MidwestMotorBoy/Battery-Bank/BatteryBank.kicad_sch

## KiCad design BatteryBank.kicad_sch (2026-10-09, an earlier design)

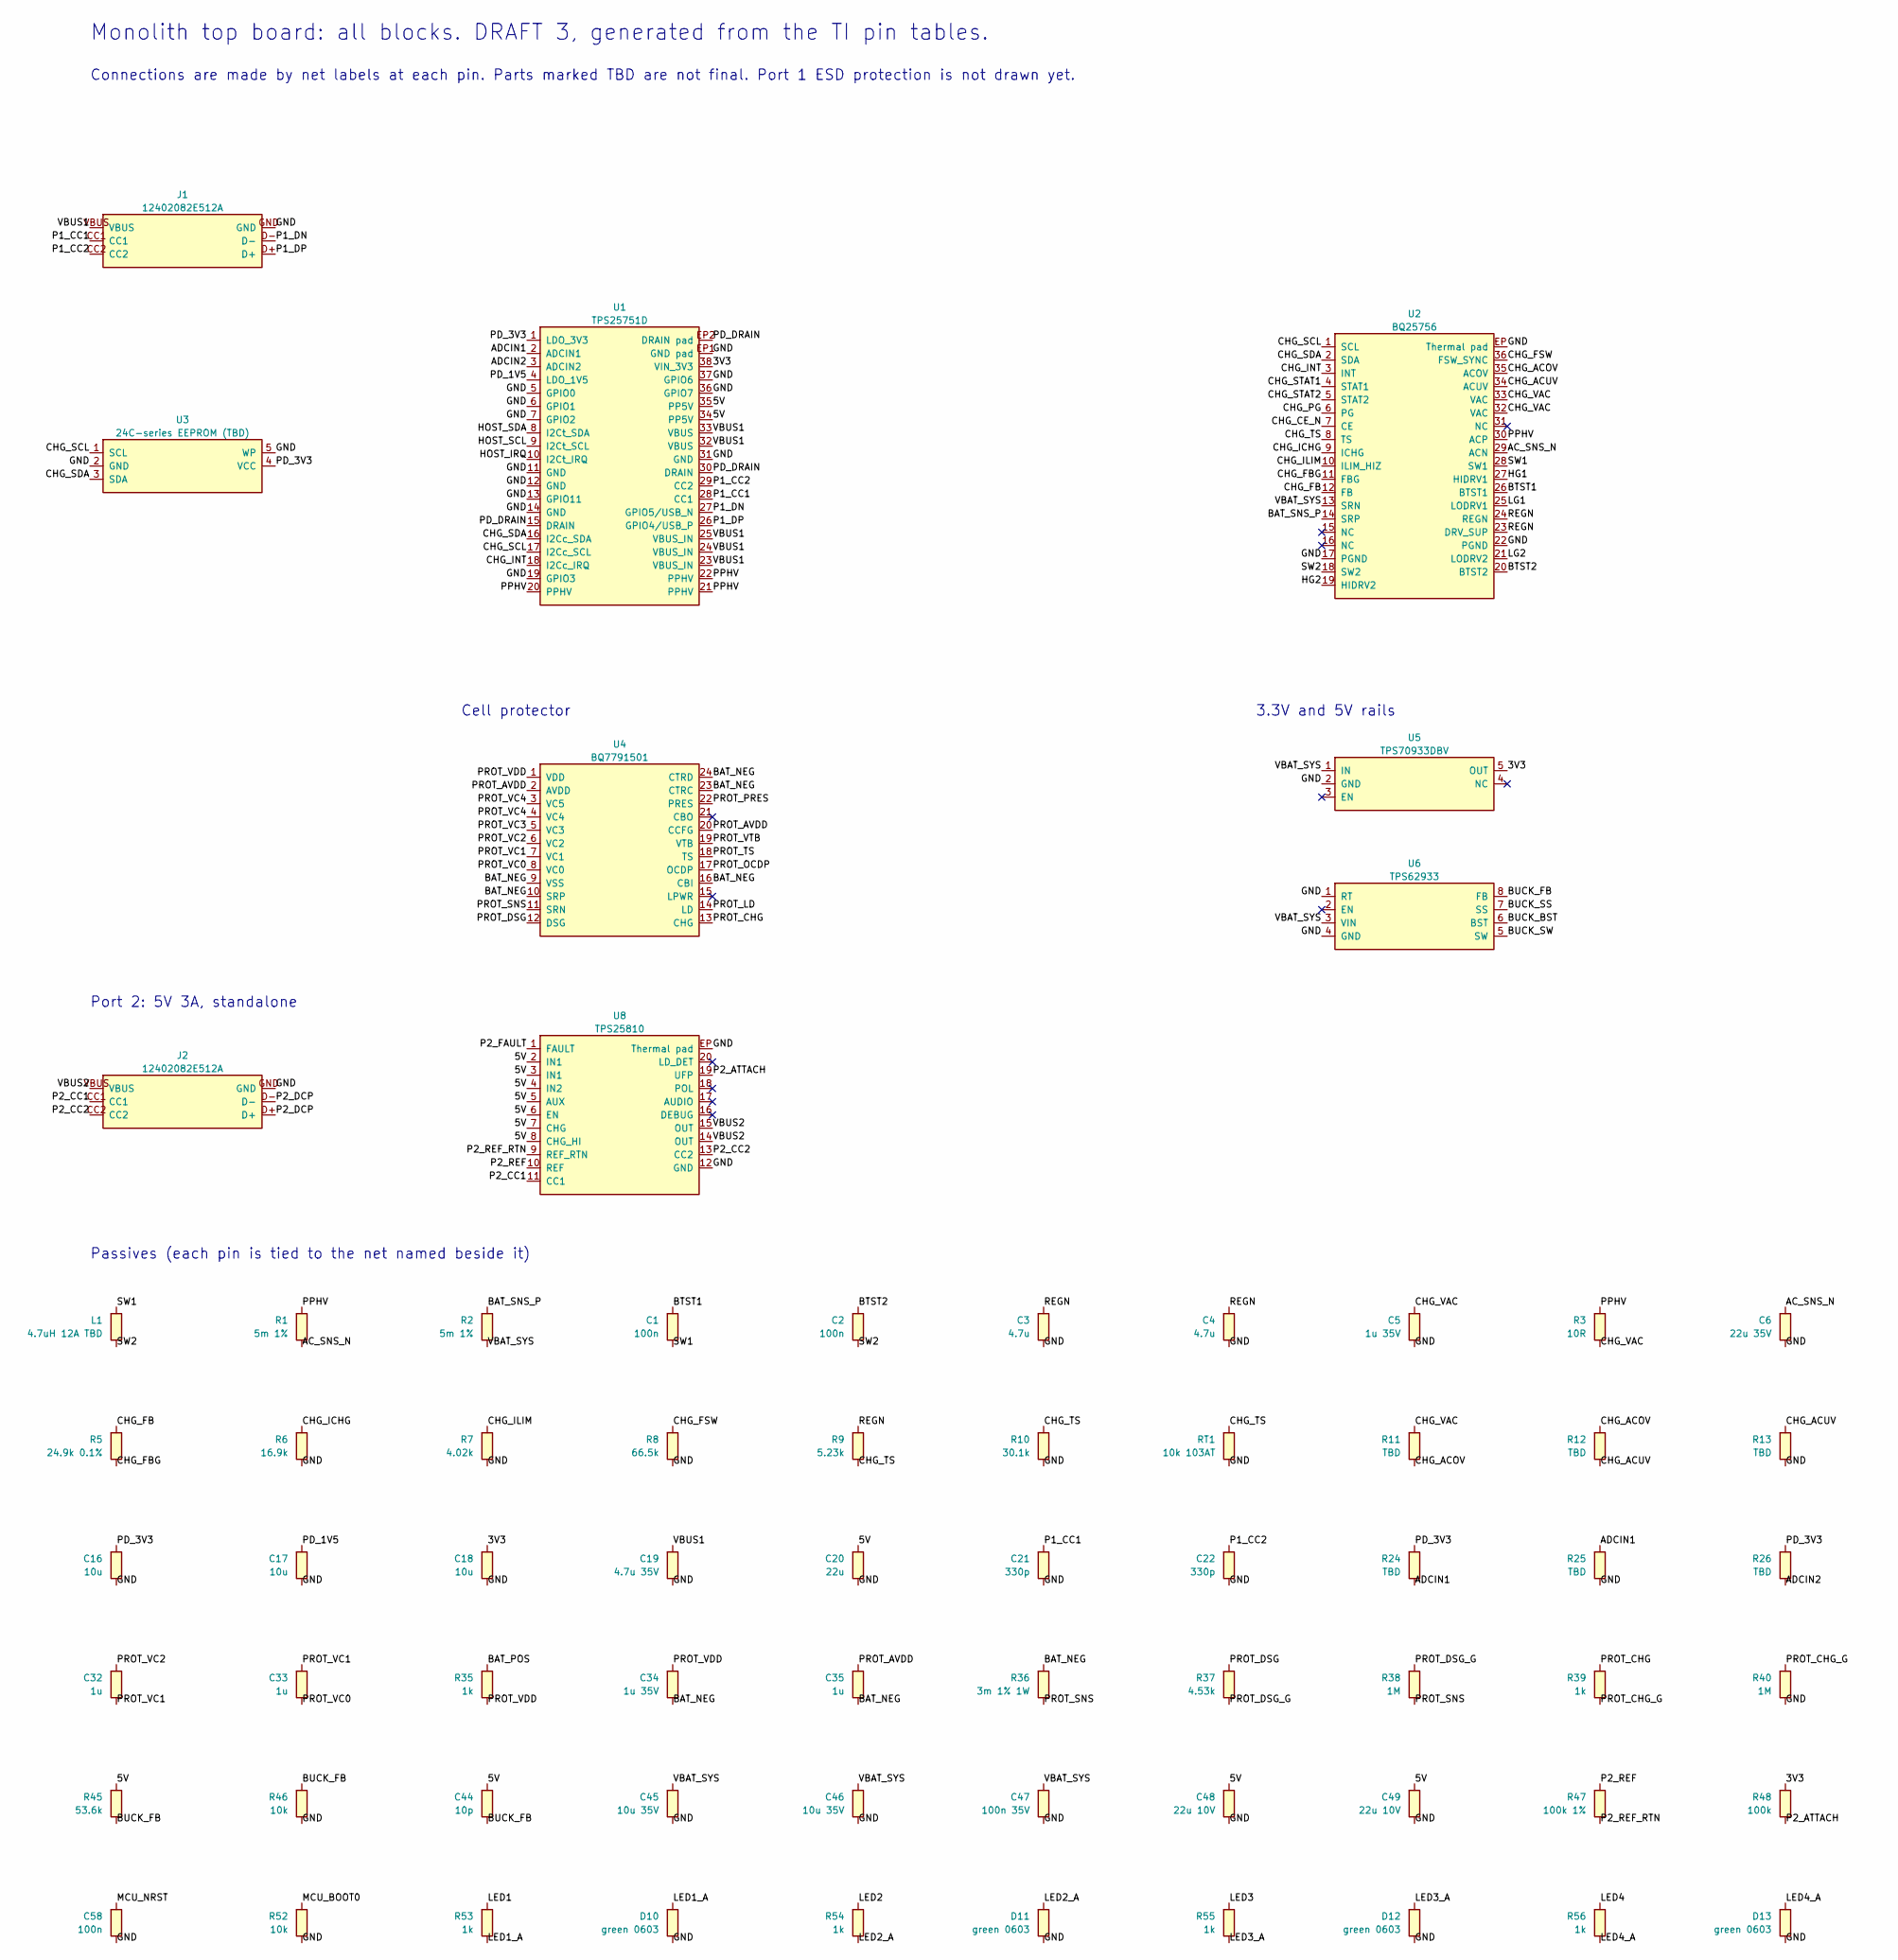
[picture p9: schematic BatteryBank.kicad_sch, part in row 1, column 1]

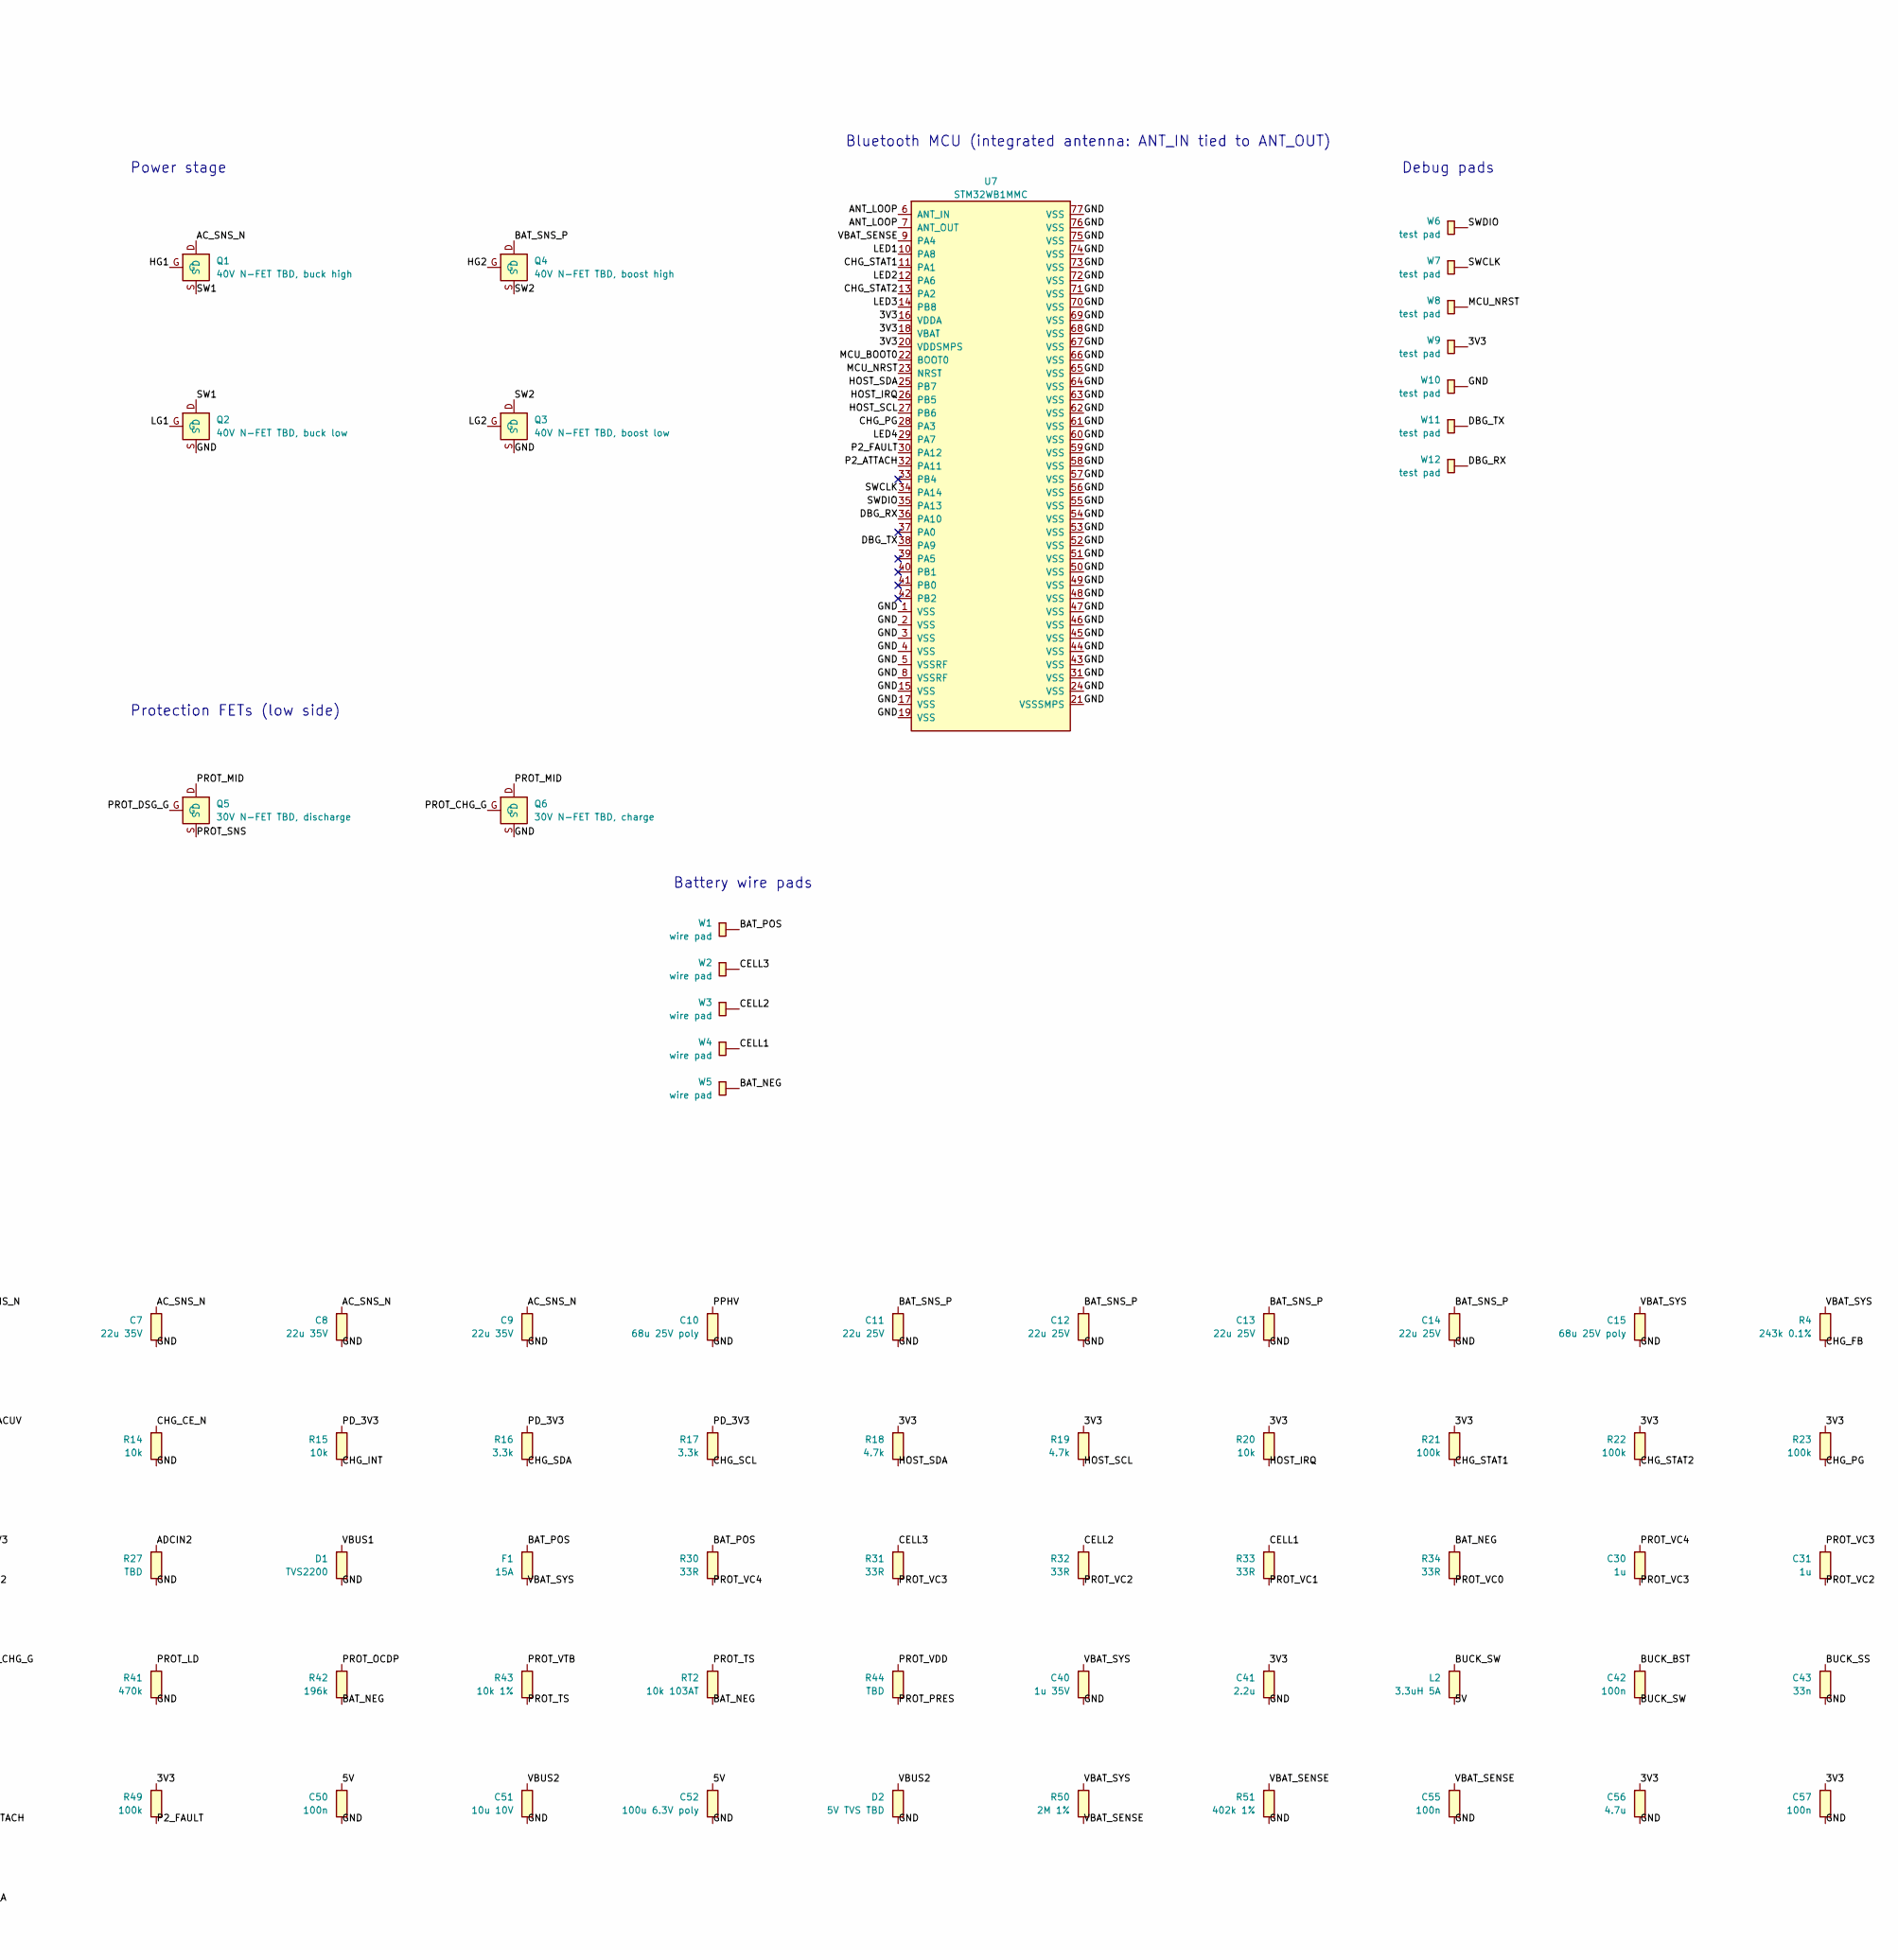
[picture p10: schematic BatteryBank.kicad_sch, part in row 1, column 2]

Parts:
C1, C2, C42, C50, C55, C57, C58: 100n
C3, C4, C56: 4.7u
C5, C34, C40: 1u 35V
C6, C7, C8, C9: 22u 35V
C10, C15: 68u 25V poly
C11, C12, C13, C14: 22u 25V
C16, C17, C18: 10u
C19: 4.7u 35V
C20: 22u
C21, C22: 330p
C30, C31, C32, C33, C35: 1u
C41: 2.2u
C43: 33n
C44: 10p
C45, C46: 10u 35V
C47: 100n 35V
C48, C49: 22u 10V
C51: 10u 10V
C52: 100u 6.3V poly
D1: TVS2200
D2: 5V TVS TBD
D10, D11, D12, D13: green 0603
F1: 15A
J1, J2: 12402082E512A
L1: 4.7uH 12A TBD
L2: 3.3uH 5A
Q1: 40V N-FET TBD, buck high
Q2: 40V N-FET TBD, buck low
Q3: 40V N-FET TBD, boost low
Q4: 40V N-FET TBD, boost high
Q5: 30V N-FET TBD, discharge
Q6: 30V N-FET TBD, charge
R1, R2: 5m 1%
R3: 10R
R4: 243k 0.1%
R5: 24.9k 0.1%
R6: 16.9k
R7: 4.02k
R8: 66.5k
R9: 5.23k
R10: 30.1k
R11, R12, R13, R24, R25, R26, R27, R44: TBD
R14, R15, R20, R46, R52: 10k
R16, R17: 3.3k
R18, R19: 4.7k
R21, R22, R23, R48, R49: 100k
R30, R31, R32, R33, R34: 33R
R35, R39, R53, R54, R55, R56: 1k
R36: 3m 1% 1W
R37: 4.53k
R38, R40: 1M
R41: 470k
R42: 196k
R43: 10k 1%
R45: 53.6k
R47: 100k 1%
R50: 2M 1%
R51: 402k 1%
RT1, RT2: 10k 103AT
U1: TPS25751D
U2: BQ25756
U3: 24C-series EEPROM (TBD)
U4: BQ7791501
U5: TPS70933DBV
U6: TPS62933
U7: STM32WB1MMC
U8: TPS25810
W1, W2, W3, W4, W5: wire pad
W6, W7, W8, W9, W10, W11, W12: test pad

Connections:
3V3: C18.1, C41.1, C56.1, C57.1, R18.1, R19.1, R20.1, R21.1, R22.1, R23.1, R48.1, R49.1, U1.38 (VIN_3V3), U5.5 (OUT), U7.16 (VDDA), U7.18 (VBAT), U7.20 (VDDSMPS), W9.1
5V: C20.1, C44.1, C48.1, C49.1, C50.1, C52.1, L2.2, R45.1, U1.34 (PP5V), U1.35 (PP5V), U8.2 (IN1), U8.3 (IN1), U8.4 (IN2), U8.5 (AUX), U8.6 (EN), U8.7 (CHG), U8.8 (CHG_HI)
AC_SNS_N: C6.1, C7.1, C8.1, C9.1, Q1.D, R1.2, U2.29 (ACN)
ADCIN1: R24.2, R25.1, U1.2 (ADCIN1)
ADCIN2: R26.2, R27.1, U1.3 (ADCIN2)
ANT_LOOP: U7.6 (ANT_IN), U7.7 (ANT_OUT)
BAT_NEG: C34.2, C35.2, R34.1, R36.1, R42.2, RT2.2, U4.9 (VSS), U4.10 (SRP), U4.16 (CBI), U4.23 (CTRC), U4.24 (CTRD), W5.1
BAT_POS: F1.1, R30.1, R35.1, W1.1
BAT_SNS_P: C11.1, C12.1, C13.1, C14.1, Q4.D, R2.1, U2.14 (SRP)
BTST1: C1.1, U2.26 (BTST1)
BTST2: C2.1, U2.20 (BTST2)
BUCK_BST: C42.1, U6.6 (BST)
BUCK_FB: C44.2, R45.2, R46.1, U6.8 (FB)
BUCK_SS: C43.1, U6.7 (SS)
BUCK_SW: C42.2, L2.1, U6.5 (SW)
CELL1: R33.1, W4.1
CELL2: R32.1, W3.1
CELL3: R31.1, W2.1
CHG_ACOV: R11.2, R12.1, U2.35 (ACOV)
CHG_ACUV: R12.2, R13.1, U2.34 (ACUV)
CHG_CE_N: R14.1, U2.7 (CE)
CHG_FB: R4.2, R5.1, U2.12 (FB)
CHG_FBG: R5.2, U2.11 (FBG)
CHG_FSW: R8.1, U2.36 (FSW_SYNC)
CHG_ICHG: R6.1, U2.9 (ICHG)
CHG_ILIM: R7.1, U2.10 (ILIM_HIZ)
CHG_INT: R15.2, U1.18 (I2Cc_IRQ), U2.3 (INT)
CHG_PG: R23.2, U2.6 (PG), U7.28 (PA3)
CHG_SCL: R17.2, U1.17 (I2Cc_SCL), U2.1 (SCL), U3.1 (SCL)
CHG_SDA: R16.2, U1.16 (I2Cc_SDA), U2.2 (SDA), U3.3 (SDA)
CHG_STAT1: R21.2, U2.4 (STAT1), U7.11 (PA1)
CHG_STAT2: R22.2, U2.5 (STAT2), U7.13 (PA2)
CHG_TS: R9.2, R10.1, RT1.1, U2.8 (TS)
CHG_VAC: C5.1, R3.2, R11.1, U2.32 (VAC), U2.33 (VAC)
DBG_RX: U7.36 (PA10), W12.1
DBG_TX: U7.38 (PA9), W11.1
GND: C3.2, C4.2, C5.2, C6.2, C7.2, C8.2, C9.2, C10.2, C11.2, C12.2, C13.2, C14.2, C15.2, C16.2, C17.2, C18.2, C19.2, C20.2, C21.2, C22.2, C40.2, C41.2, C43.2, C45.2, C46.2, C47.2, C48.2, C49.2, C50.2, C51.2, C52.2, C55.2, C56.2, C57.2, C58.2, D1.2, D2.2, D10.2, D11.2, D12.2, D13.2, J1.GND, J2.GND, Q2.S, Q3.S, Q6.S, R6.2, R7.2, R8.2, R10.2, R13.2, R14.2, R25.2, R27.2, R40.2, R41.2, R46.2, R51.2, R52.2, RT1.2, U1.5 (GPIO0), U1.6 (GPIO1), U1.7 (GPIO2), U1.11 (GND), U1.12 (GND), U1.13 (GPIO11), U1.14 (GND), U1.19 (GPIO3), U1.31 (GND), U1.36 (GPIO7), U1.37 (GPIO6), U1.EP1 (GND pad), U2.17 (PGND), U2.22 (PGND), U2.EP (Thermal pad), U3.2 (GND), U3.5 (WP), U5.2 (GND), U6.1 (RT), U6.4 (GND), U7.1 (VSS), U7.2 (VSS), U7.3 (VSS), U7.4 (VSS), U7.5 (VSSRF), U7.8 (VSSRF), U7.15 (VSS), U7.17 (VSS), U7.19 (VSS), U7.21 (VSSSMPS), U7.24 (VSS), U7.31 (VSS), U7.43 (VSS), U7.44 (VSS), U7.45 (VSS), U7.46 (VSS), U7.47 (VSS), U7.48 (VSS), U7.49 (VSS), U7.50 (VSS), U7.51 (VSS), U7.52 (VSS), U7.53 (VSS), U7.54 (VSS), U7.55 (VSS), U7.56 (VSS), U7.57 (VSS), U7.58 (VSS), U7.59 (VSS), U7.60 (VSS), U7.61 (VSS), U7.62 (VSS), U7.63 (VSS), U7.64 (VSS), U7.65 (VSS), U7.66 (VSS), U7.67 (VSS), U7.68 (VSS), U7.69 (VSS), U7.70 (VSS), U7.71 (VSS), U7.72 (VSS), U7.73 (VSS), U7.74 (VSS), U7.75 (VSS), U7.76 (VSS), U7.77 (VSS), U8.12 (GND), U8.EP (Thermal pad), W10.1
HG1: Q1.G, U2.27 (HIDRV1)
HG2: Q4.G, U2.19 (HIDRV2)
HOST_IRQ: R20.2, U1.10 (I2Ct_IRQ), U7.26 (PB5)
HOST_SCL: R19.2, U1.9 (I2Ct_SCL), U7.27 (PB6)
HOST_SDA: R18.2, U1.8 (I2Ct_SDA), U7.25 (PB7)
LED1: R53.1, U7.10 (PA8)
LED1_A: D10.1, R53.2
LED2: R54.1, U7.12 (PA6)
LED2_A: D11.1, R54.2
LED3: R55.1, U7.14 (PB8)
LED3_A: D12.1, R55.2
LED4: R56.1, U7.29 (PA7)
LED4_A: D13.1, R56.2
LG1: Q2.G, U2.25 (LODRV1)
LG2: Q3.G, U2.21 (LODRV2)
MCU_BOOT0: R52.1, U7.22 (BOOT0)
MCU_NRST: C58.1, U7.23 (NRST), W8.1
P1_CC1: C21.1, J1.CC1, U1.28 (CC1)
P1_CC2: C22.1, J1.CC2, U1.29 (CC2)
P1_DN: J1.D-, U1.27 (GPIO5/USB_N)
P1_DP: J1.D+, U1.26 (GPIO4/USB_P)
P2_ATTACH: R48.2, U7.32 (PA11), U8.19 (UFP)
P2_CC1: J2.CC1, U8.11 (CC1)
P2_CC2: J2.CC2, U8.13 (CC2)
P2_DCP: J2.D+, J2.D-
P2_FAULT: R49.2, U7.30 (PA12), U8.1 (FAULT)
P2_REF: R47.1, U8.10 (REF)
P2_REF_RTN: R47.2, U8.9 (REF_RTN)
PD_1V5: C17.1, U1.4 (LDO_1V5)
PD_3V3: C16.1, R15.1, R16.1, R17.1, R24.1, R26.1, U1.1 (LDO_3V3), U3.4 (VCC)
PD_DRAIN: U1.15 (DRAIN), U1.30 (DRAIN), U1.EP2 (DRAIN pad)
PPHV: C10.1, R1.1, R3.1, U1.20 (PPHV), U1.21 (PPHV), U1.22 (PPHV), U2.30 (ACP)
PROT_AVDD: C35.1, U4.2 (AVDD), U4.20 (CCFG)
PROT_CHG: R39.1, U4.13 (CHG)
PROT_CHG_G: Q6.G, R39.2, R40.1
PROT_DSG: R37.1, U4.12 (DSG)
PROT_DSG_G: Q5.G, R37.2, R38.1
PROT_LD: R41.1, U4.14 (LD)
PROT_MID: Q5.D, Q6.D
PROT_OCDP: R42.1, U4.17 (OCDP)
PROT_PRES: R44.2, U4.22 (PRES)
PROT_SNS: Q5.S, R36.2, R38.2, U4.11 (SRN)
PROT_TS: R43.2, RT2.1, U4.18 (TS)
PROT_VC0: C33.2, R34.2, U4.8 (VC0)
PROT_VC1: C32.2, C33.1, R33.2, U4.7 (VC1)
PROT_VC2: C31.2, C32.1, R32.2, U4.6 (VC2)
PROT_VC3: C30.2, C31.1, R31.2, U4.5 (VC3)
PROT_VC4: C30.1, R30.2, U4.3 (VC5), U4.4 (VC4)
PROT_VDD: C34.1, R35.2, R44.1, U4.1 (VDD)
PROT_VTB: R43.1, U4.19 (VTB)
REGN: C3.1, C4.1, R9.1, U2.23 (DRV_SUP), U2.24 (REGN)
SW1: C1.2, L1.1, Q1.S, Q2.D, U2.28 (SW1)
SW2: C2.2, L1.2, Q3.D, Q4.S, U2.18 (SW2)
SWCLK: U7.34 (PA14), W7.1
SWDIO: U7.35 (PA13), W6.1
VBAT_SENSE: C55.1, R50.2, R51.1, U7.9 (PA4)
VBAT_SYS: C15.1, C40.1, C45.1, C46.1, C47.1, F1.2, R2.2, R4.1, R50.1, U2.13 (SRN), U5.1 (IN), U6.3 (VIN)
VBUS1: C19.1, D1.1, J1.VBUS, U1.23 (VBUS_IN), U1.24 (VBUS_IN), U1.25 (VBUS_IN), U1.32 (VBUS), U1.33 (VBUS)
VBUS2: C51.1, D2.1, J2.VBUS, U8.14 (OUT), U8.15 (OUT)

Notes on the sheet:
Monolith top board: all blocks. DRAFT 3, generated from the TI pin tables.
Connections are made by net labels at each pin. Parts marked TBD are not final. Port 1 ESD protection is not drawn yet.
Power stage
Cell protector
3.3V and 5V rails
Protection FETs (low side)
Battery wire pads
Bluetooth MCU (integrated antenna: ANT_IN tied to ANT_OUT)
Debug pads
Port 2: 5V 3A, standalone
Passives (each pin is tied to the net named beside it)
